hnz1102/dcpower/doc/adaptor1-pcb.png

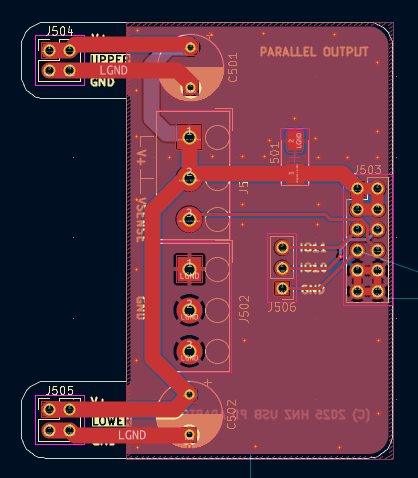
doc/adaptor1-pcb.png
