hnz1102/dcpower/doc/adaptor2-pcb.png

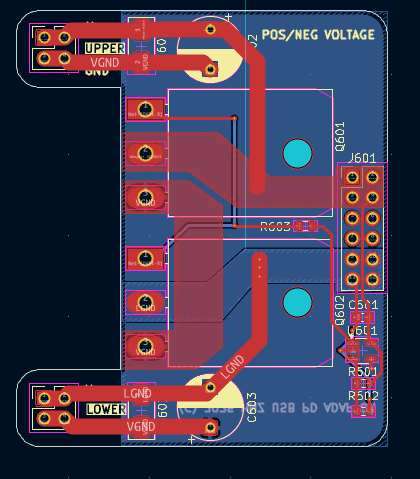
doc/adaptor2-pcb.png
