hnz1102/dcpower/doc/pcbway.png

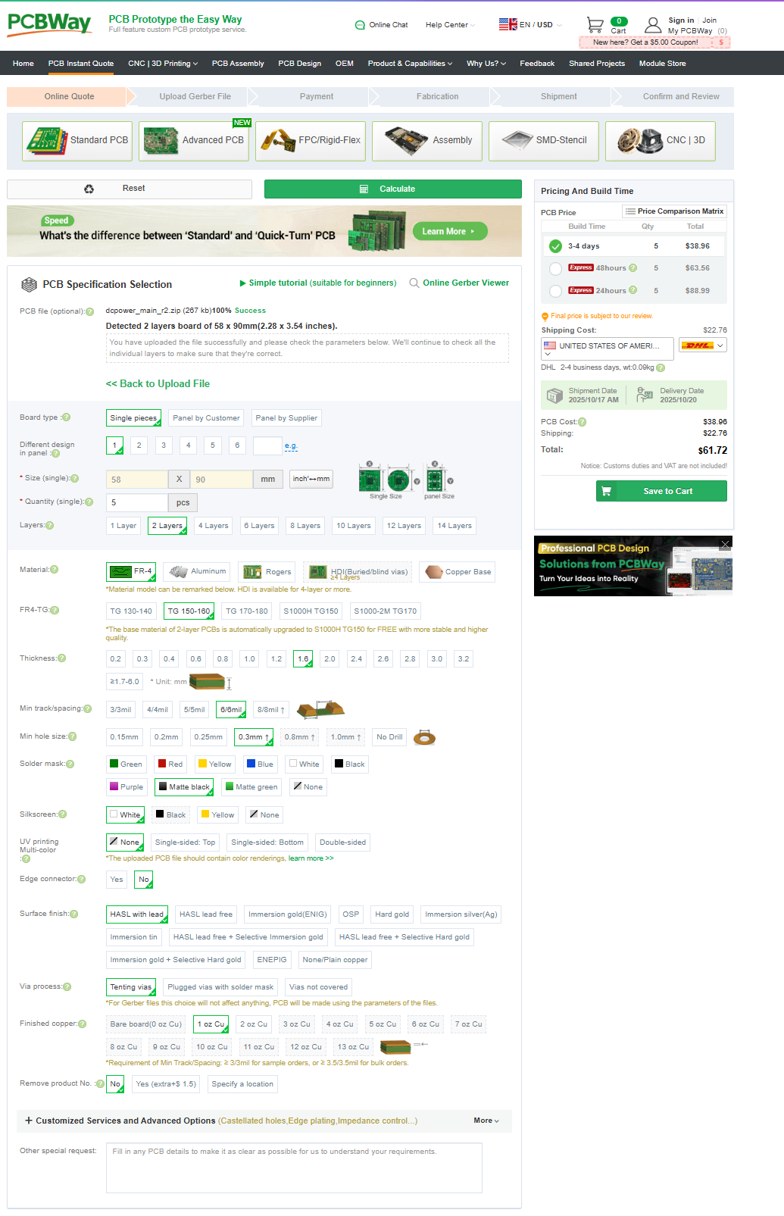
doc/pcbway.png
